ianmott77/wireless-timer/Arduino/ConnectionV2/Packet.h

#ifndef PACKET_H
#define PACKET_H

#include <Arduino.h>
enum DataType{INT = 0, FLOAT = 1, LONG = 2, ULONG = 3, STRING = 4};

class Packet{
	public:
		Packet(void*, DataType, int);
        ~Packet();
		int size;
		void * data;
		DataType dataType;
};

#endif
